Aidan-McNay/5220-telehealth/lorawan/lorawan.h

// =======================================================================
// lorawan.h
// =======================================================================
// Declarations of our LoRaWAN interface

#ifndef LORAWAN_LORAWAN_H
#define LORAWAN_LORAWAN_H

#include "LmHandler.h"
#include "lorawan/lorawan_config.h"
#include <cstdint>

void confirm();  // Called to confirm a message

class LoRaWAN {
  // - - - - - - - - - - - - - - - - - - - - - - - - - - - - - - - - - - -
  // Public Accessor Functions
  // - - - - - - - - - - - - - - - - - - - - - - - - - - - - - - - - - - -
 public:
  LoRaWAN();

  // Return whether joining is successful
  bool try_join();

  // Return whether sending the message is successful
  bool try_send( const uint8_t* data, uint8_t data_len );

  // Call to confirm a message has been sent
  void confirm();

  // - - - - - - - - - - - - - - - - - - - - - - - - - - - - - - - - - - -
  // Private Functions
  // - - - - - - - - - - - - - - - - - - - - - - - - - - - - - - - - - - -
 private:
  int send_confirmed( const void* data, uint8_t data_len,
                      uint8_t app_port );

  // - - - - - - - - - - - - - - - - - - - - - - - - - - - - - - - - - - -
  // Protected Attributes
  // - - - - - - - - - - - - - - - - - - - - - - - - - - - - - - - - - - -
 protected:
  bool join_started;
  bool msg_sent;
  bool msg_confirmed;
};

#endif  // LORAWAN_LORAWAN_H
